patrickMelo/portatil/Software/Runtime/Assets.c

//
// Runtime/Assets.c
//
// This file is part of Portatil source code.
// Copyright 2025 Patrick L. Melo <patrick@patrickmelo.com.br>
//

#include "Assets.h"

// clang-format off

static const byte ScrollDownImageData[] = {
    0x00, 0x00, 0x00, 0x00, 0x00, 0x00, 0x00, 
    0x00, 0x00, 0x00, 0x00, 0x00, 0x00, 0x00, 
    0x00, 0x0F, 0x0F, 0x0F, 0x0F, 0x0F, 0x00, 
    0x00, 0x00, 0x0F, 0x0F, 0x0F, 0x00, 0x00, 
    0x00, 0x00, 0x00, 0x0F, 0x00, 0x00, 0x00, 
    0x00, 0x00, 0x00, 0x00, 0x00, 0x00, 0x00, 
    0x00, 0x00, 0x00, 0x00, 0x00, 0x00, 0x00, 
    };

const Image ScrollDownImage = {
    .Width = 7, 
    .Height = 7, 
    .Data = (byte*) ScrollDownImageData,
};

const Rectangle2D ScrollDownRectangle = {
    .X = 0,
    .Y = 0,
    .Width = 7,
    .Height = 7,
};

static const byte FolderIconImageData[] = {
    0x00, 0x00, 0x00, 0x00, 0x00, 0x00, 0x00, 
    0x00, 0x44, 0x44, 0x44, 0x00, 0x00, 0x00, 
    0x44, 0x4B, 0x4B, 0x4A, 0x44, 0x44, 0x44, 
    0x44, 0x4B, 0x4A, 0x4A, 0x4A, 0x46, 0x44, 
    0x44, 0x4A, 0x4A, 0x4A, 0x46, 0x46, 0x44, 
    0x44, 0x4A, 0x4A, 0x46, 0x46, 0x46, 0x44, 
    0x44, 0x44, 0x44, 0x44, 0x44, 0x44, 0x44, 
    };

const Image FolderIconImage = {
    .Width = 7, 
    .Height = 7, 
    .Data = (byte*) FolderIconImageData,
};

const Rectangle2D FolderIconRectangle = {
    .X = 0,
    .Y = 0,
    .Width = 7,
    .Height = 7,
};

static const byte BatteryImageData[] = {
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
    };

const Image DefaultFontImage = {
    .Width = 96, 
    .Height = 64, 
    .Data = (byte*) DefaultFontImageData,
};

const Rectangle2D DefaultFontRectangle = {
    .X = 0,
    .Y = 0,
    .Width = 96,
    .Height = 64,
};

static const byte ProgramIconImageData[] = {
    0x00, 0x00, 0x00, 0x00, 0x00, 0x00, 0x00, 
    0xD3, 0xD3, 0xD3, 0xD3, 0xD3, 0xD3, 0xD3, 
    0xD3, 0xD9, 0xD8, 0xD7, 0xD6, 0xD5, 0xD3, 
    0x03, 0x0F, 0x0C, 0x09, 0x07, 0x06, 0x03, 
    0x03, 0x0F, 0x0C, 0x09, 0x07, 0x06, 0x03, 
    0x03, 0x0F, 0x0C, 0x09, 0x07, 0x06, 0x03, 
    0x03, 0x03, 0x03, 0x03, 0x03, 0x03, 0x03, 
    };

const Image ProgramIconImage = {
    .Width = 7, 
    .Height = 7, 
    .Data = (byte*) ProgramIconImageData,
};

const Rectangle2D ProgramIconRectangle = {
    .X = 0,
    .Y = 0,
    .Width = 7,
    .Height = 7,
};

// clang-format on
