patrickMelo/portatil/Software/Runtime/Assets.h

//
// Runtime/Assets.h
//
// This file is part of Portatil source code.
// Copyright 2025 Patrick L. Melo <patrick@patrickmelo.com.br>
//

#ifndef PORTATIL_ASSETS_H
#define PORTATIL_ASSETS_H

#include "Kernel.h"

extern const Image       ScrollDownImage;
extern const Rectangle2D ScrollDownRectangle;
extern const Image       FolderIconImage;
extern const Rectangle2D FolderIconRectangle;
extern const Image       BatteryImage;
extern const Rectangle2D BatteryRectangle;
extern const Image       ScrollUpImage;
extern const Rectangle2D ScrollUpRectangle;
extern const Image       DefaultFontImage;
extern const Rectangle2D DefaultFontRectangle;
extern const Image       ProgramIconImage;
extern const Rectangle2D ProgramIconRectangle;

#endif    // PORTATIL_ASSETS_H
